CedarGroveStudios/Stemma_Host_FeatherWing/photos/Stemma_Host_FeatherWing_close.png

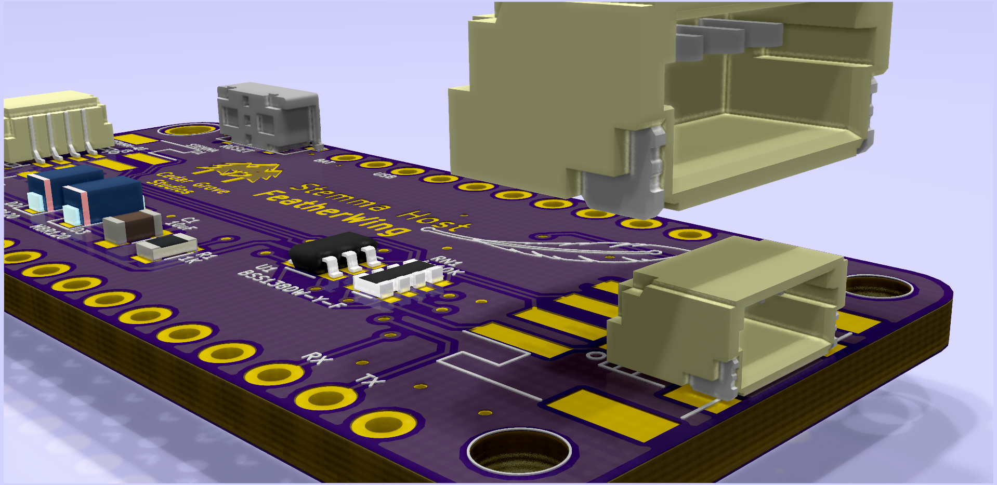
photos/Stemma_Host_FeatherWing_close.png
